brooksware2000/Hobbybotics-Reflow-Controller/Hardware/Hobbybotics LED Panel/Pictures/Hobbybotics LED Panel V1.00 - Schematic_3060x2310.png

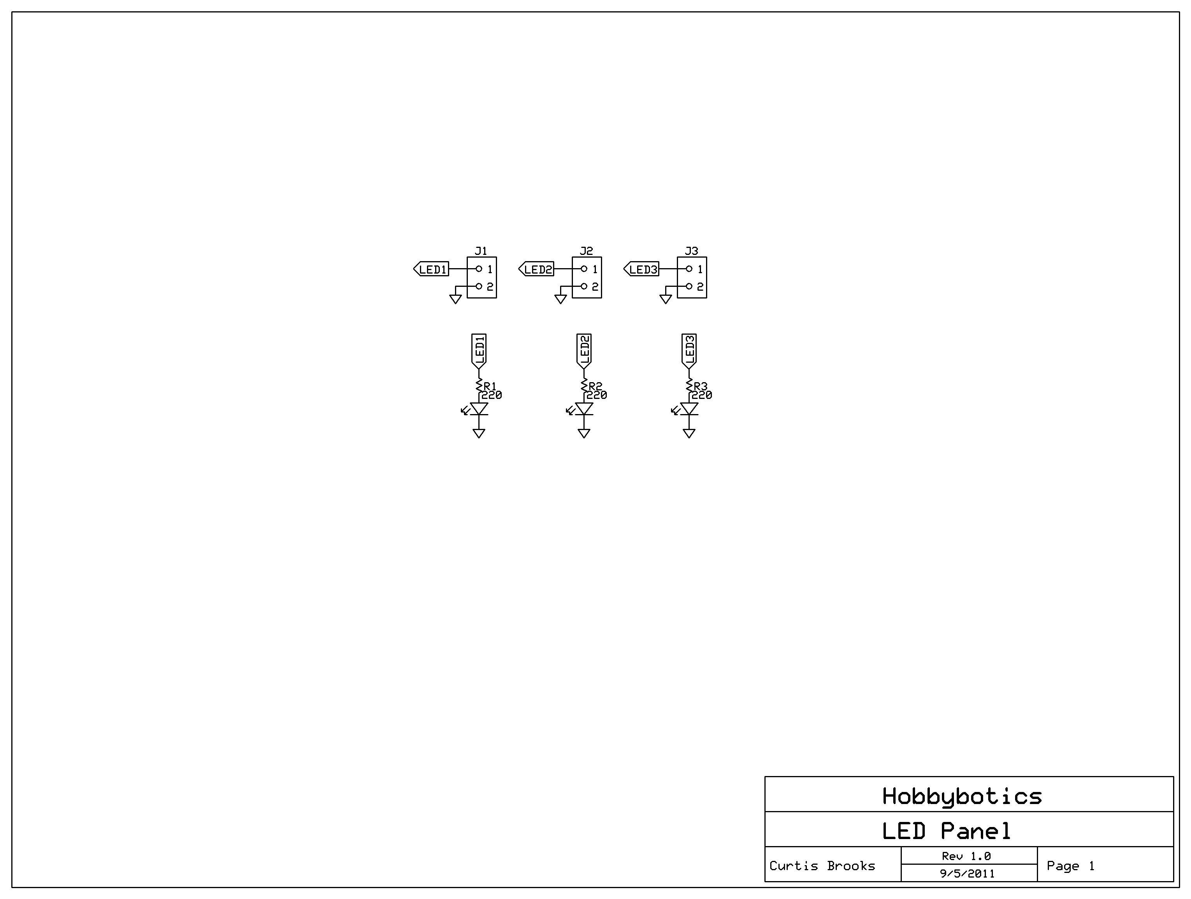
Hardware/Hobbybotics LED Panel/Pictures/Hobbybotics LED Panel V1.00 - Schematic_3060x2310.png
