brooksware2000/Hobbybotics-Reflow-Controller/Hardware/HobbyboticsSwitch Panel/Pictures/DSCN0554.JPG

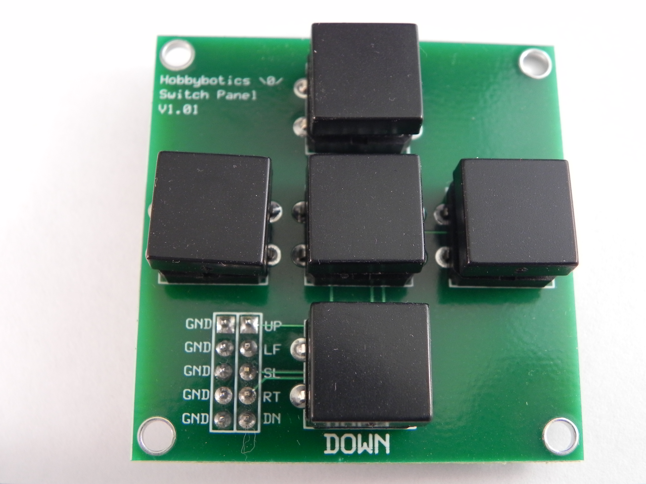
Hardware/HobbyboticsSwitch Panel/Pictures/DSCN0554.JPG
