brooksware2000/Hobbybotics-Reflow-Controller/Hardware/HobbyboticsSwitch Panel/Pictures/Hobbybotics Switch Panel V1.01 (Production)_638x652.png

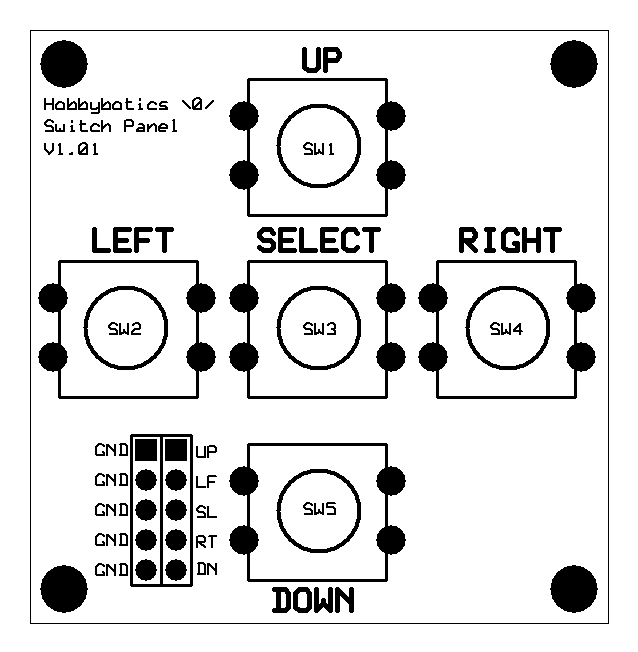
Hardware/HobbyboticsSwitch Panel/Pictures/Hobbybotics Switch Panel V1.01 (Production)_638x652.png
