brooksware2000/Hobbybotics-Reflow-Controller/Hardware/HobbyboticsSwitch Panel/Pictures/Hobbybotics Switch Panel V1.01_1200x810.png

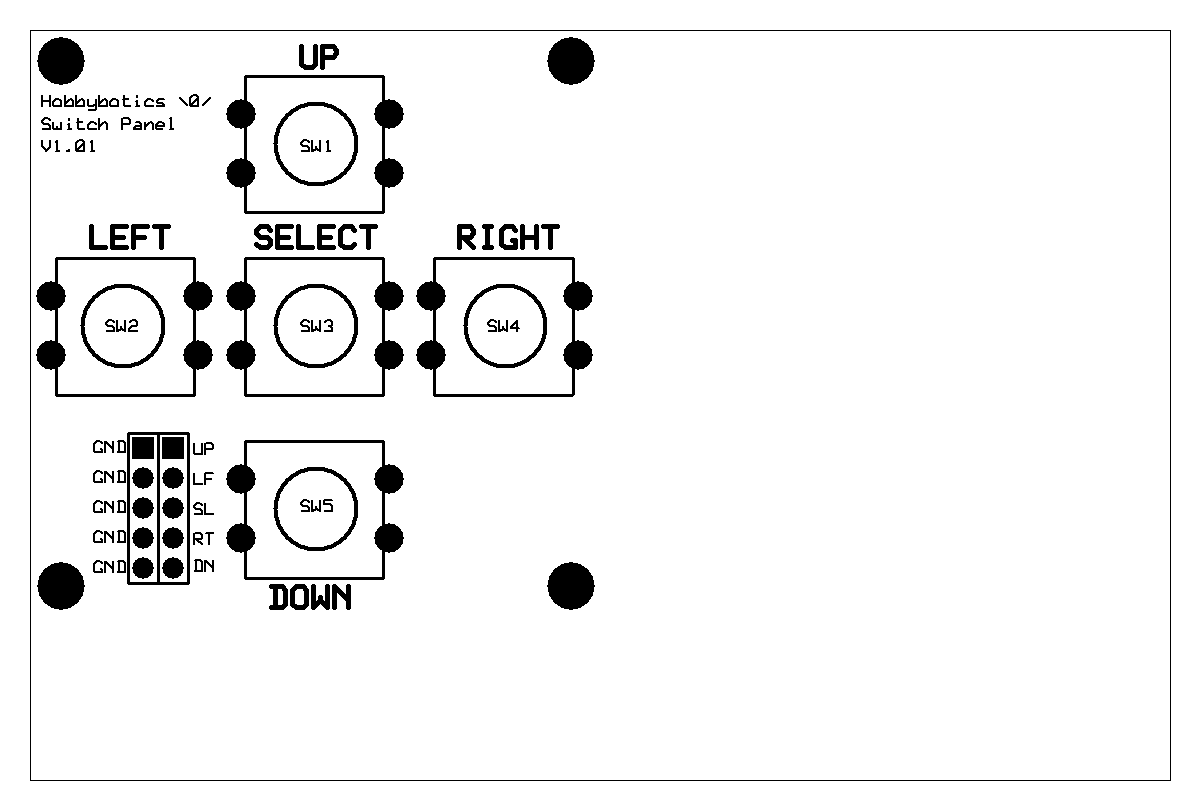
Hardware/HobbyboticsSwitch Panel/Pictures/Hobbybotics Switch Panel V1.01_1200x810.png
