brooksware2000/Hobbybotics-Reflow-Controller/Hardware/Main Board/Reflow Controller V8.03 (Mechanical Drawing).png

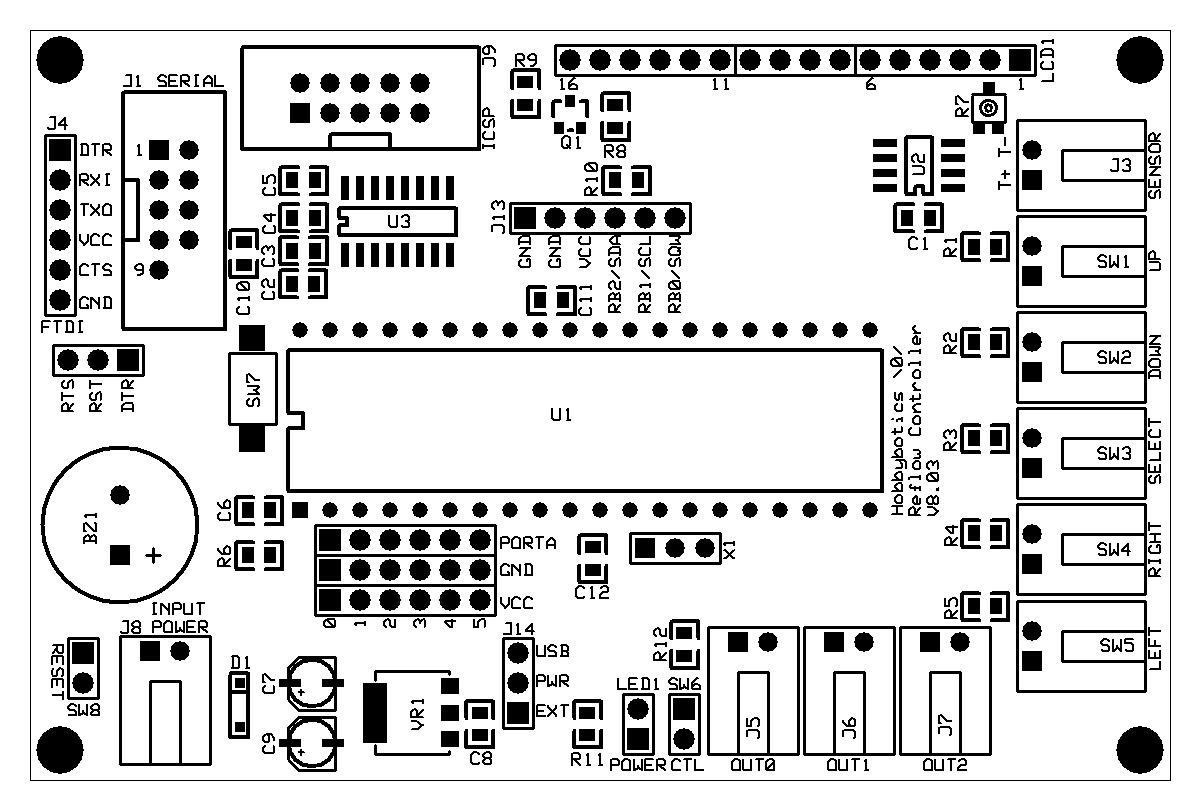
Hardware/Main Board/Reflow Controller V8.03 (Mechanical Drawing).png
